DennisRathgeb/doppler-radar-detector/hardware/simulations/MF_bandpass.asc

C1: cap; 150p
C2: cap; 150p
C3: cap; 56n
C4: cap; 3.3n
C5: cap; 10µ
C7: cap; 1µ
C8: cap; 1µ
C9: cap; 56n
C10: cap; 3.3n
C11: cap; 100µ
R1: res; 1000
R2: res; 10k
R3: res; 5.6k
R4: res; 8.2k
R5: res; 8.2k
R6: res; 1000
R7: res; 4.7k
R8: res; 4.7k
R9: res; 10k
R10: res; 5.6k
R11: res; 8.2k
R12: res; 1k
U1: AD8033
U2: MCP6001_AB
U4: MCP6001_AB
U6: MCP6001_AB
V1: voltage; SINE(0 3 20000); AC 1V
V2: voltage; 10
V3: voltage; 10
V4: voltage; 3
Named nets: 0, -V, +V, +3V, V_Radar_Out, V_Bandpass_1, V_Bandpass_2, V_ADC_IN
.lib opamp.sub
.ac dec 1000 10 1000000
.meas vmax max v(v_Adc_in)
